Emparans/AWSD/Codigo/deteccion_de_objetos/modelo/BoxP_curve.png

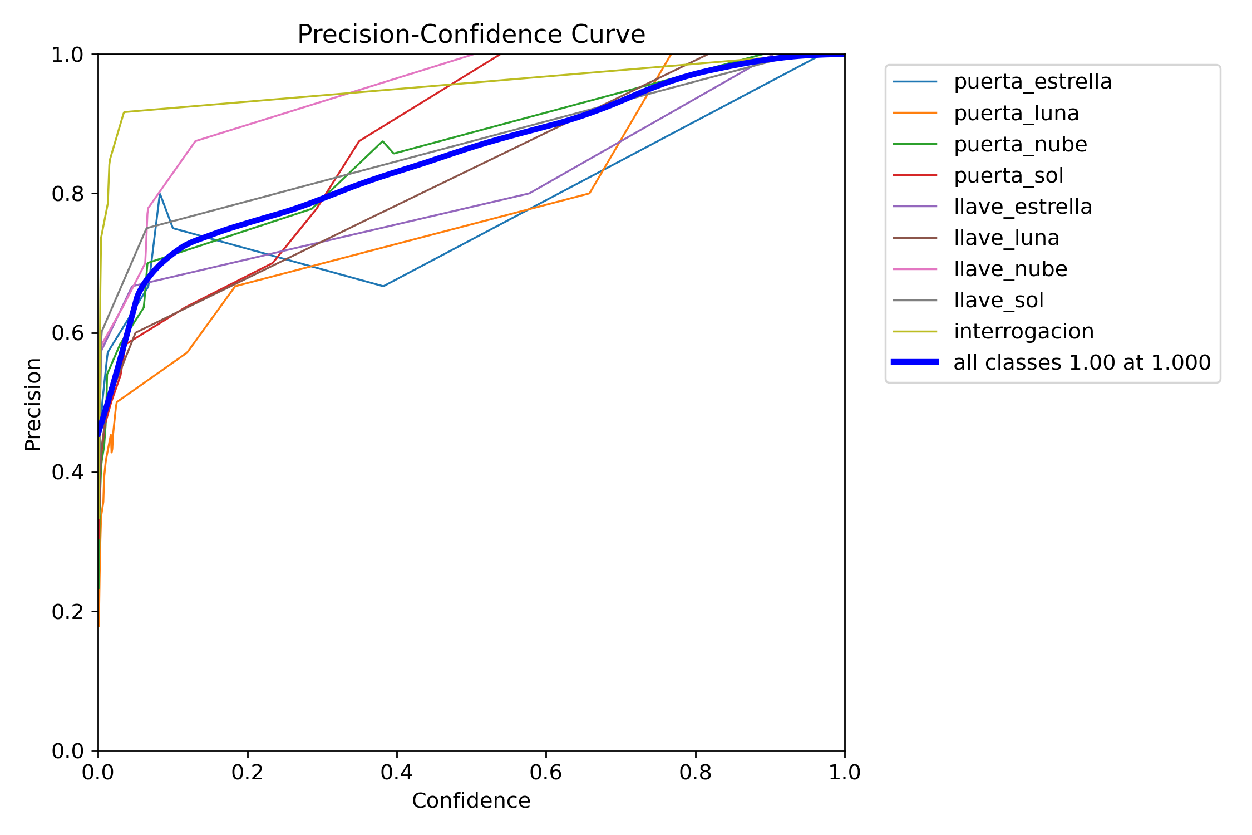
Codigo/deteccion_de_objetos/modelo/BoxP_curve.png
