Emparans/AWSD/Codigo/deteccion_de_objetos/modelo/BoxPR_curve.png

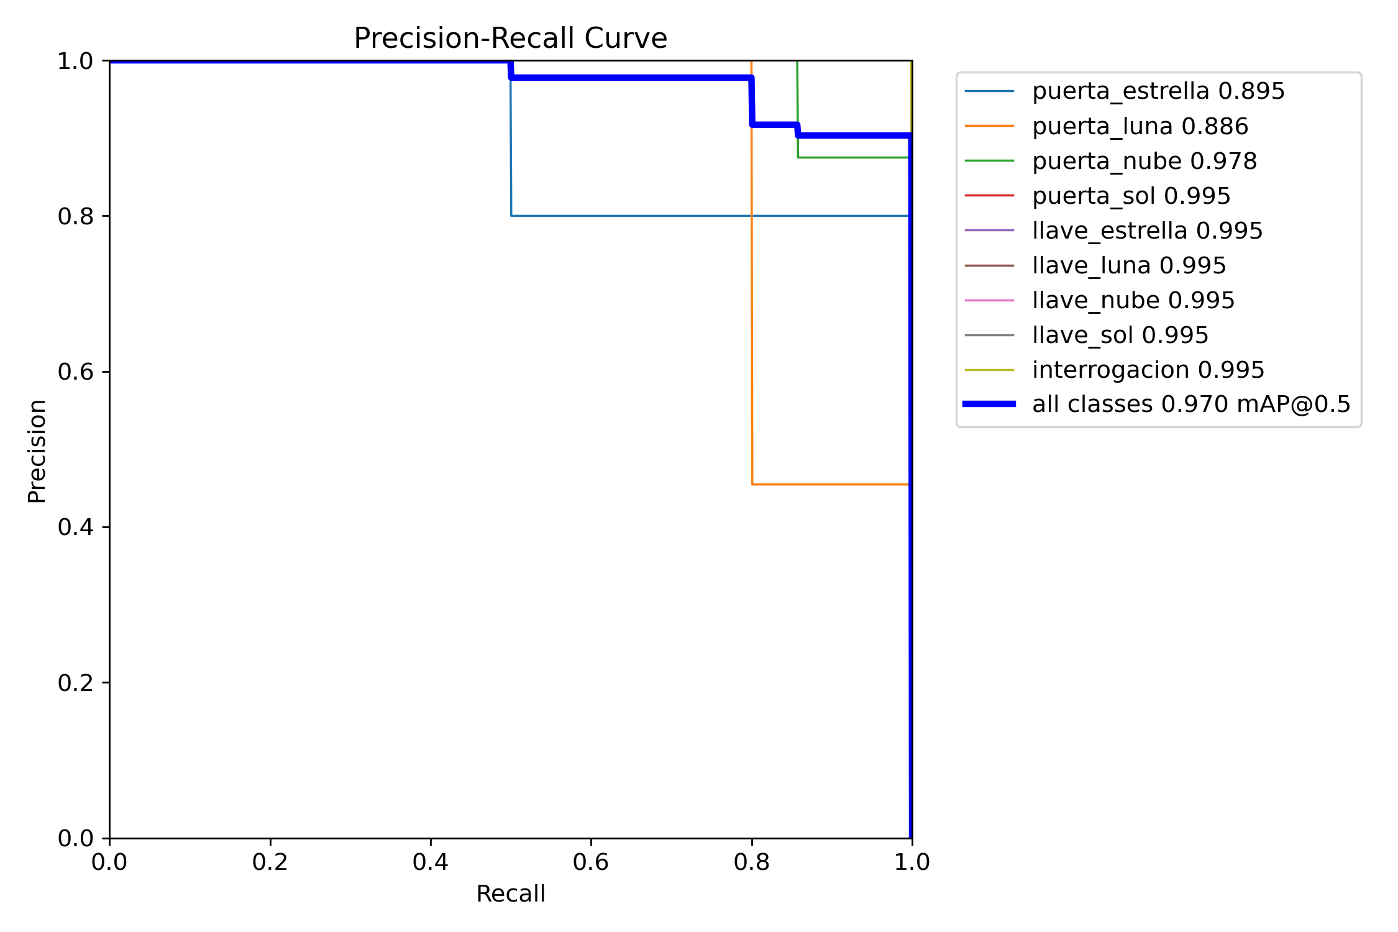
Codigo/deteccion_de_objetos/modelo/BoxPR_curve.png
