Emparans/AWSD/Codigo/deteccion_de_objetos/modelo/BoxR_curve.png

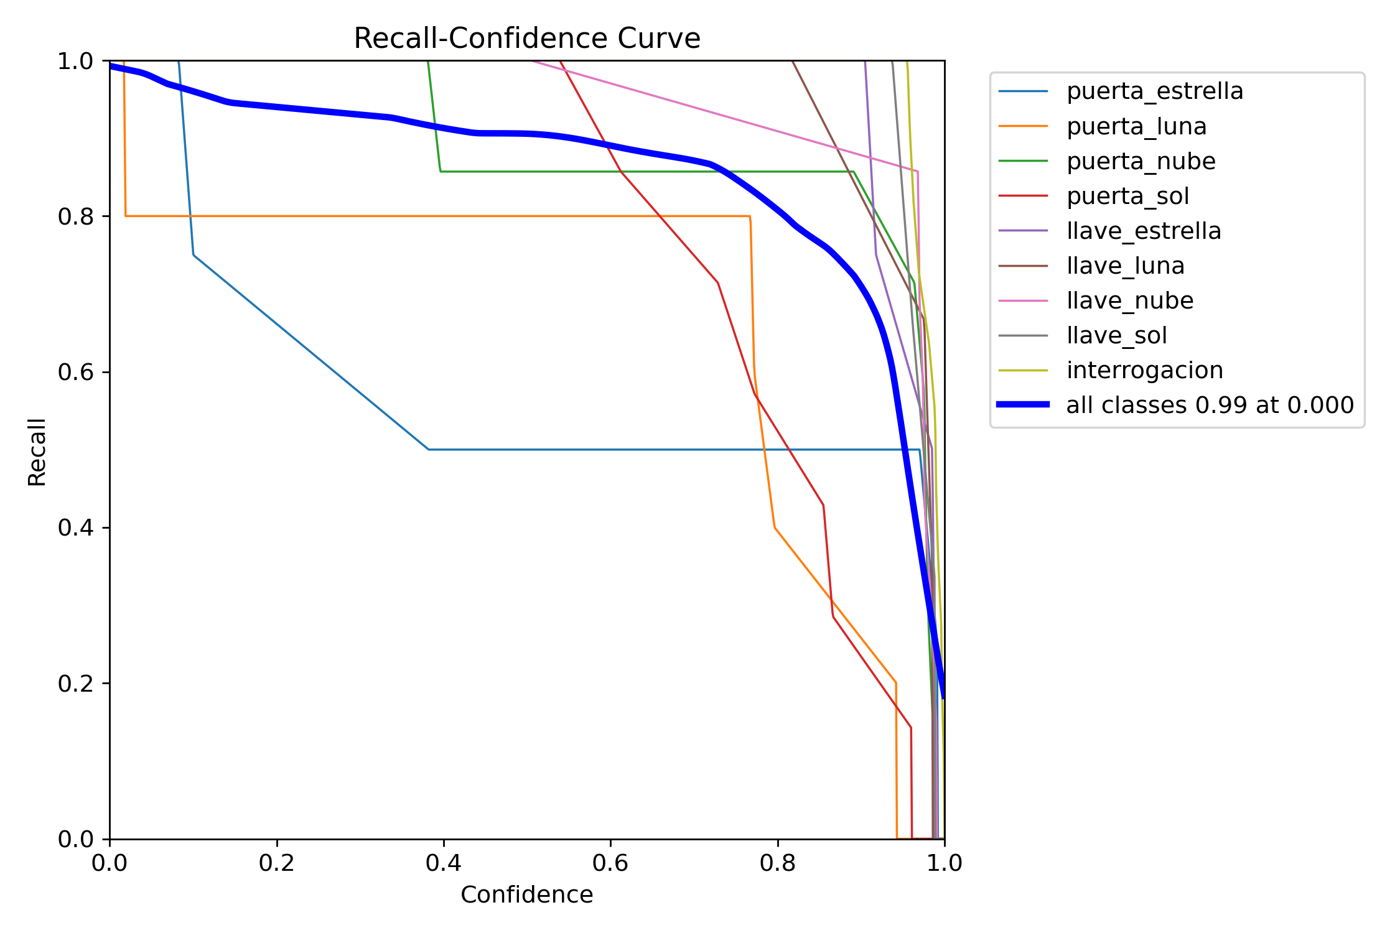
Codigo/deteccion_de_objetos/modelo/BoxR_curve.png
