Emparans/AWSD/Codigo/deteccion_de_objetos/modelo/confusion_matrix.png

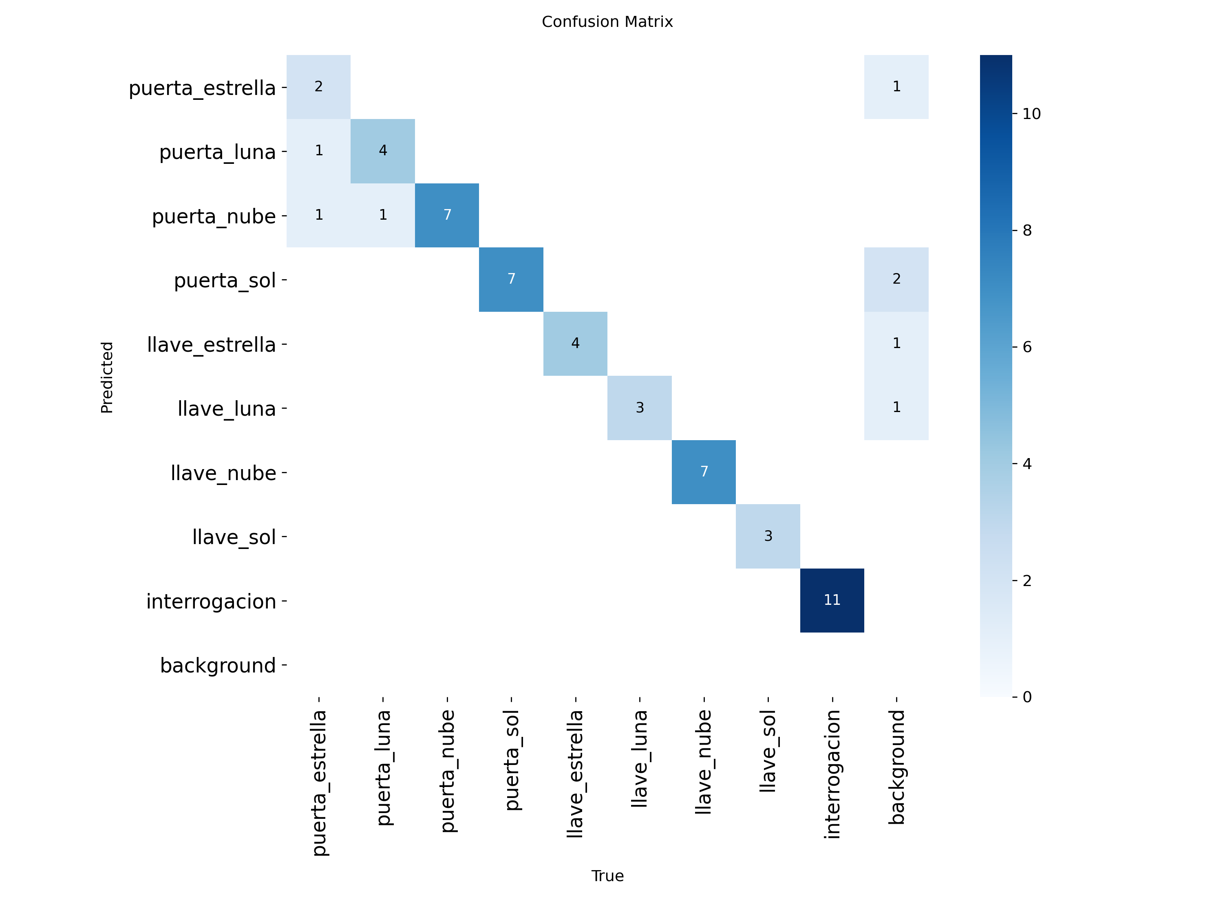
Codigo/deteccion_de_objetos/modelo/confusion_matrix.png
