Emparans/AWSD/Codigo/deteccion_de_objetos/modelo/labels.jpg

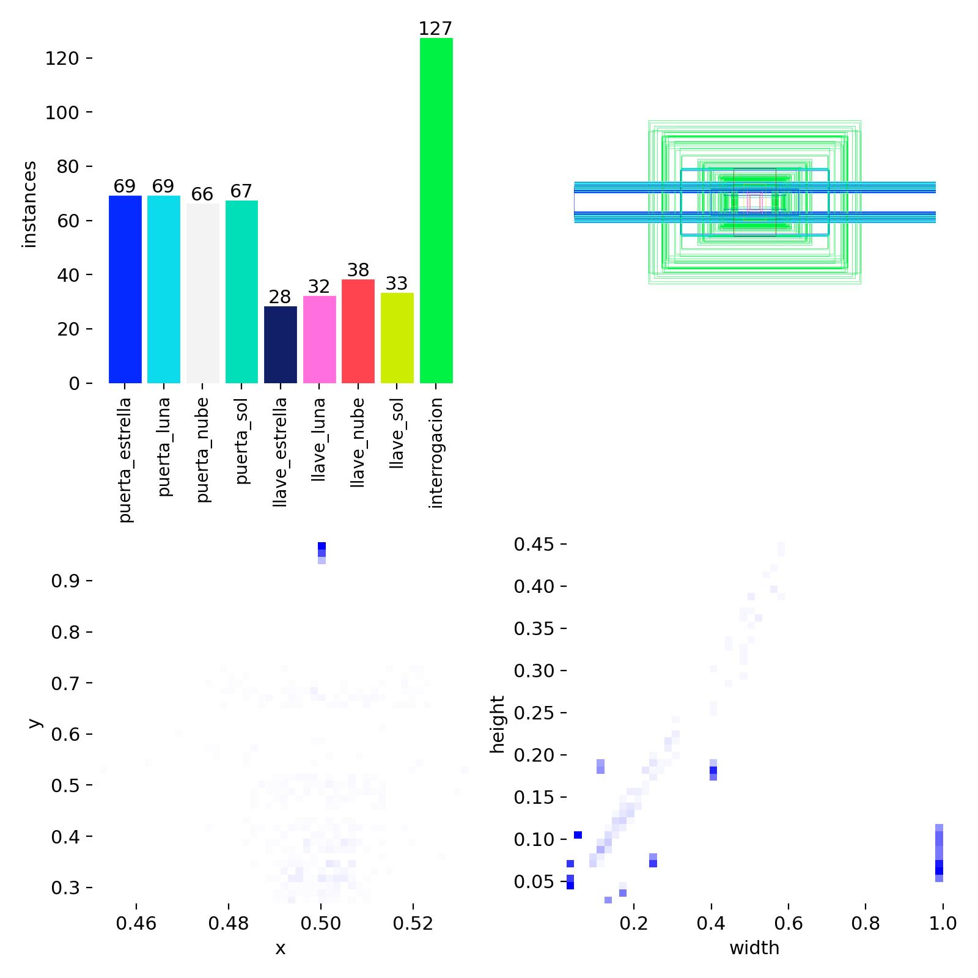
Codigo/deteccion_de_objetos/modelo/labels.jpg
