Emparans/AWSD/Codigo/deteccion_de_objetos/modelo/train_batch0.jpg

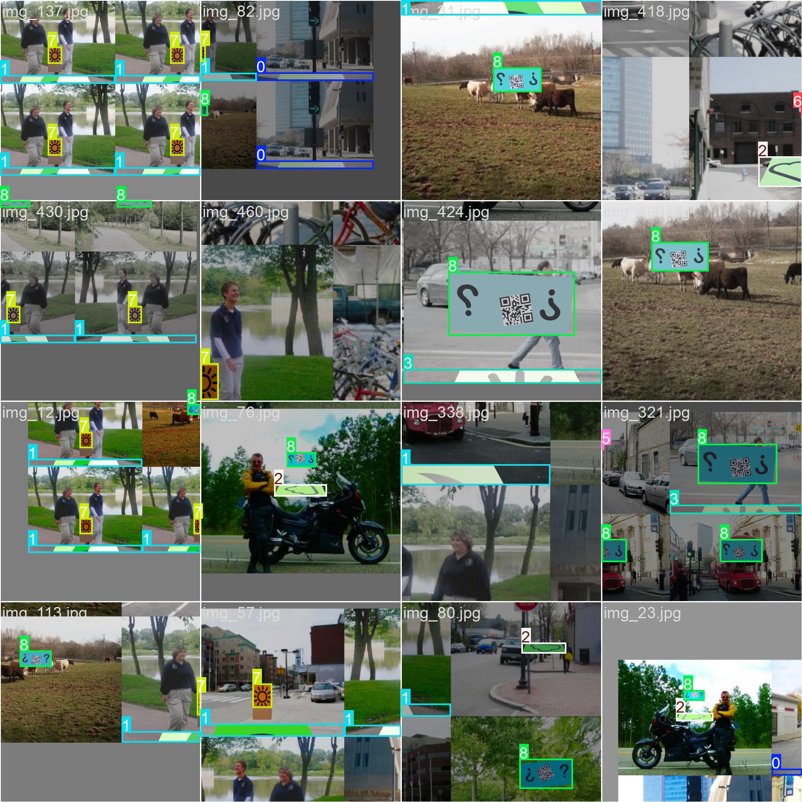
Codigo/deteccion_de_objetos/modelo/train_batch0.jpg
