Emparans/AWSD/Codigo/deteccion_de_objetos/modelo/train_batch1.jpg

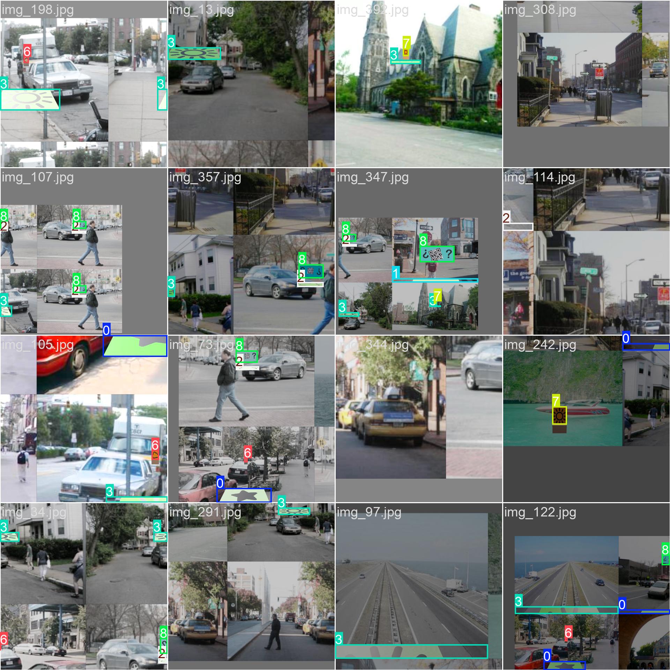
Codigo/deteccion_de_objetos/modelo/train_batch1.jpg
