Emparans/AWSD/Codigo/deteccion_de_objetos/modelo/train_batch2.jpg

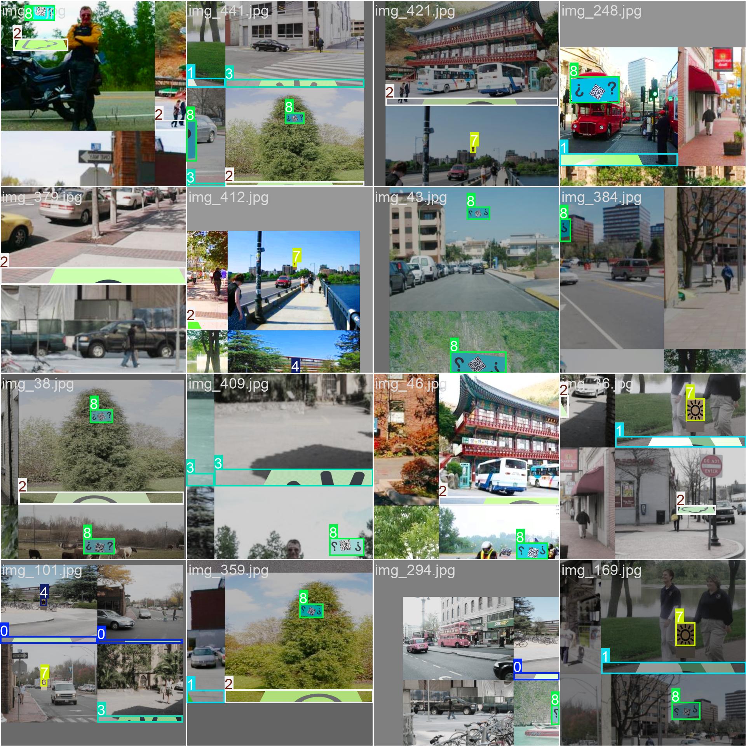
Codigo/deteccion_de_objetos/modelo/train_batch2.jpg
