Emparans/AWSD/Codigo/deteccion_de_objetos/modelo/train_batch1281.jpg

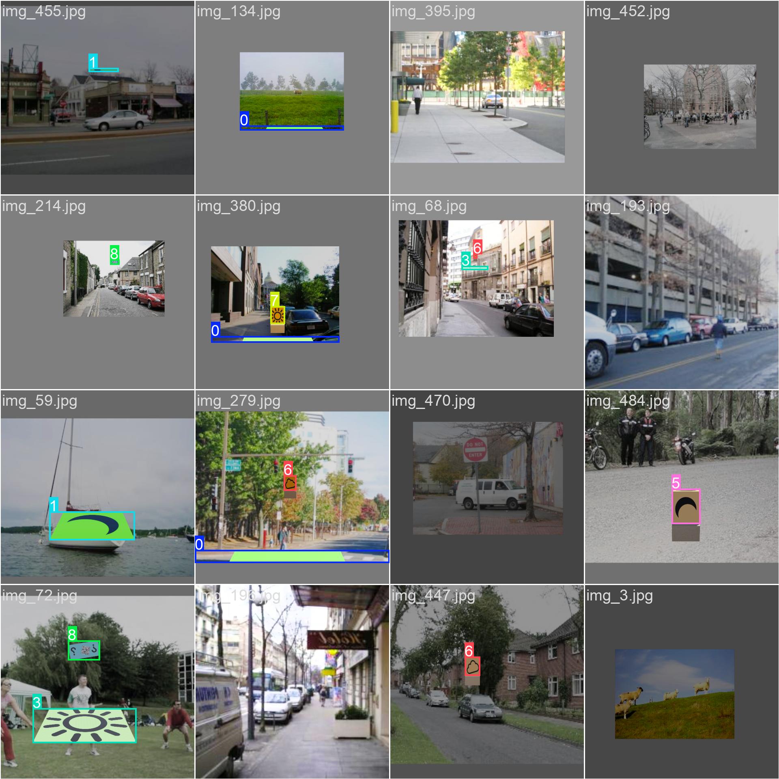
Codigo/deteccion_de_objetos/modelo/train_batch1281.jpg
