Emparans/AWSD/Codigo/deteccion_de_objetos/modelo/val/BoxF1_curve.png

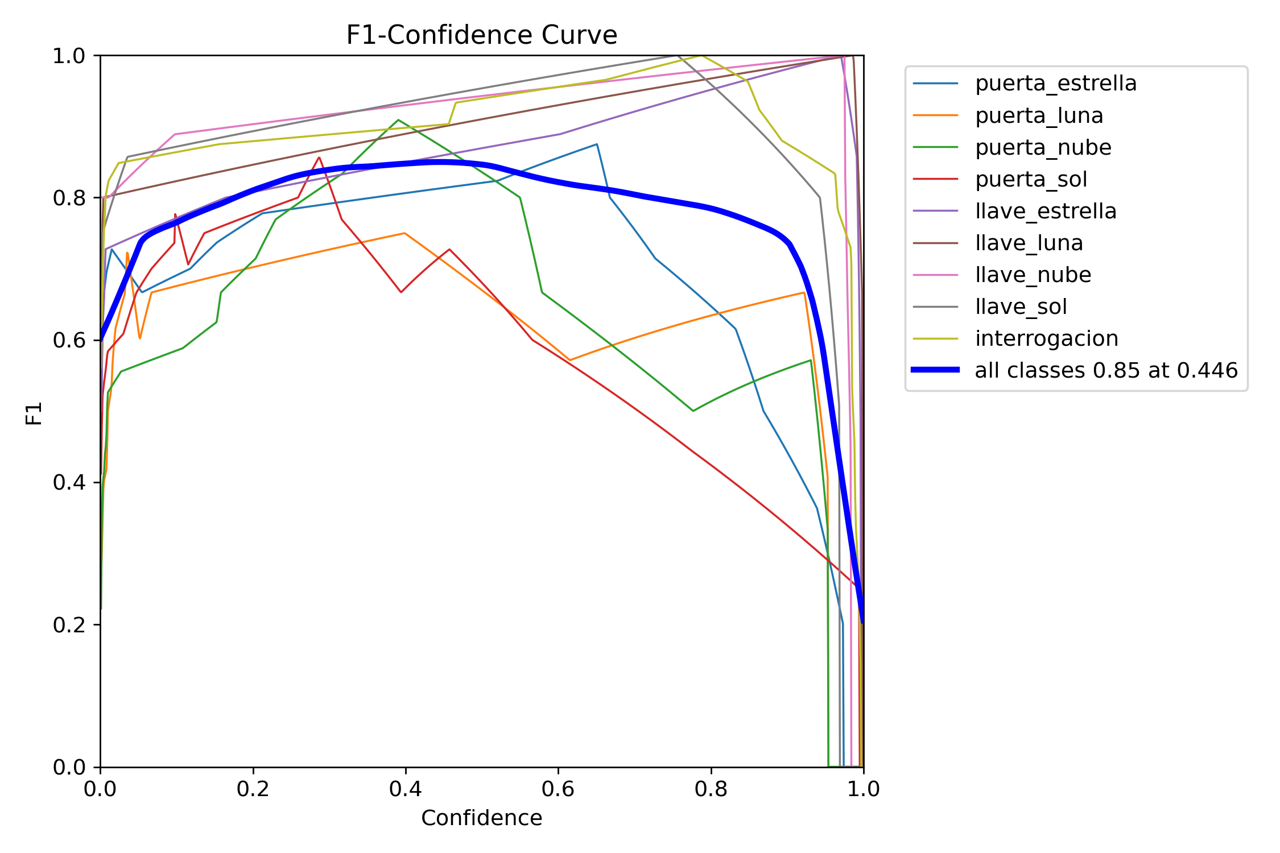
Codigo/deteccion_de_objetos/modelo/val/BoxF1_curve.png
