Emparans/AWSD/Codigo/deteccion_de_objetos/modelo/val/BoxP_curve.png

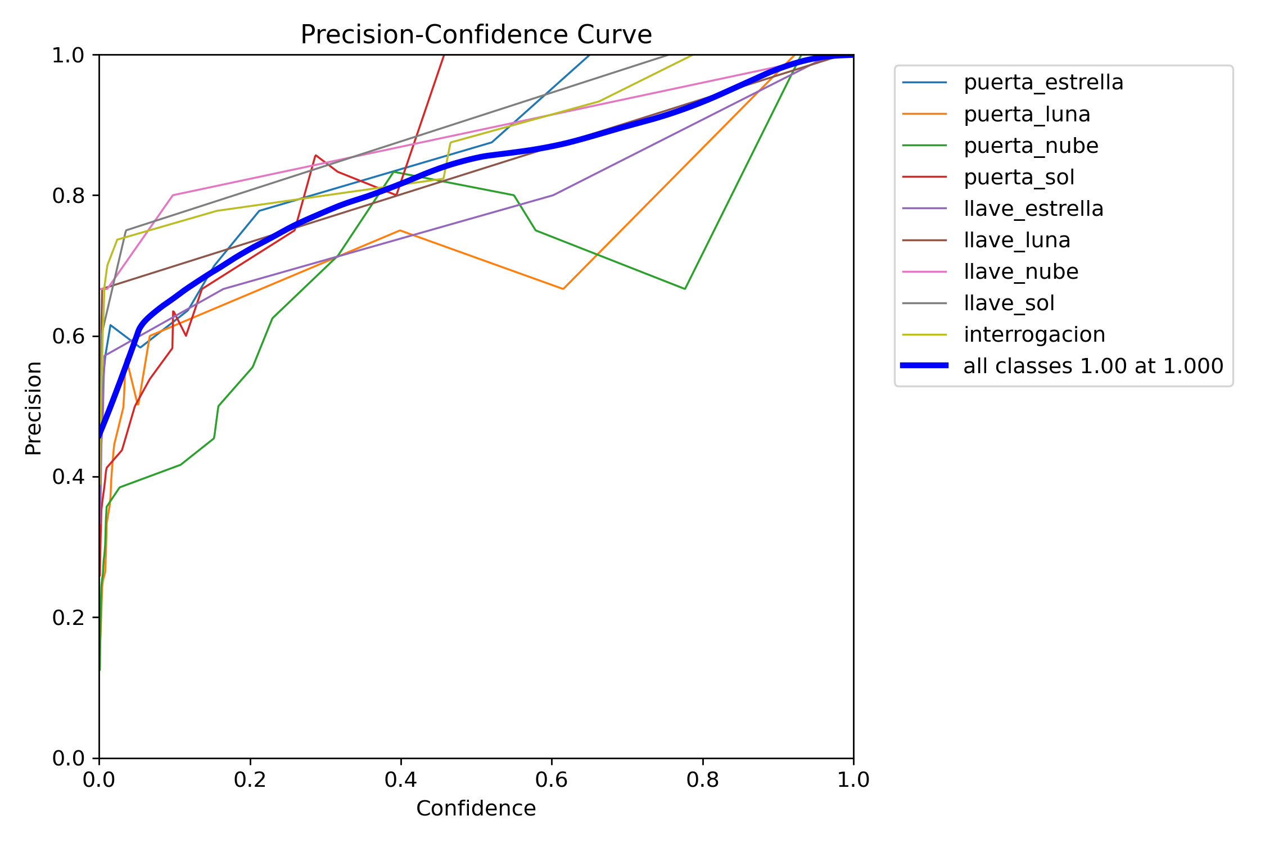
Codigo/deteccion_de_objetos/modelo/val/BoxP_curve.png
