Emparans/AWSD/Codigo/deteccion_de_objetos/modelo/val/BoxR_curve.png

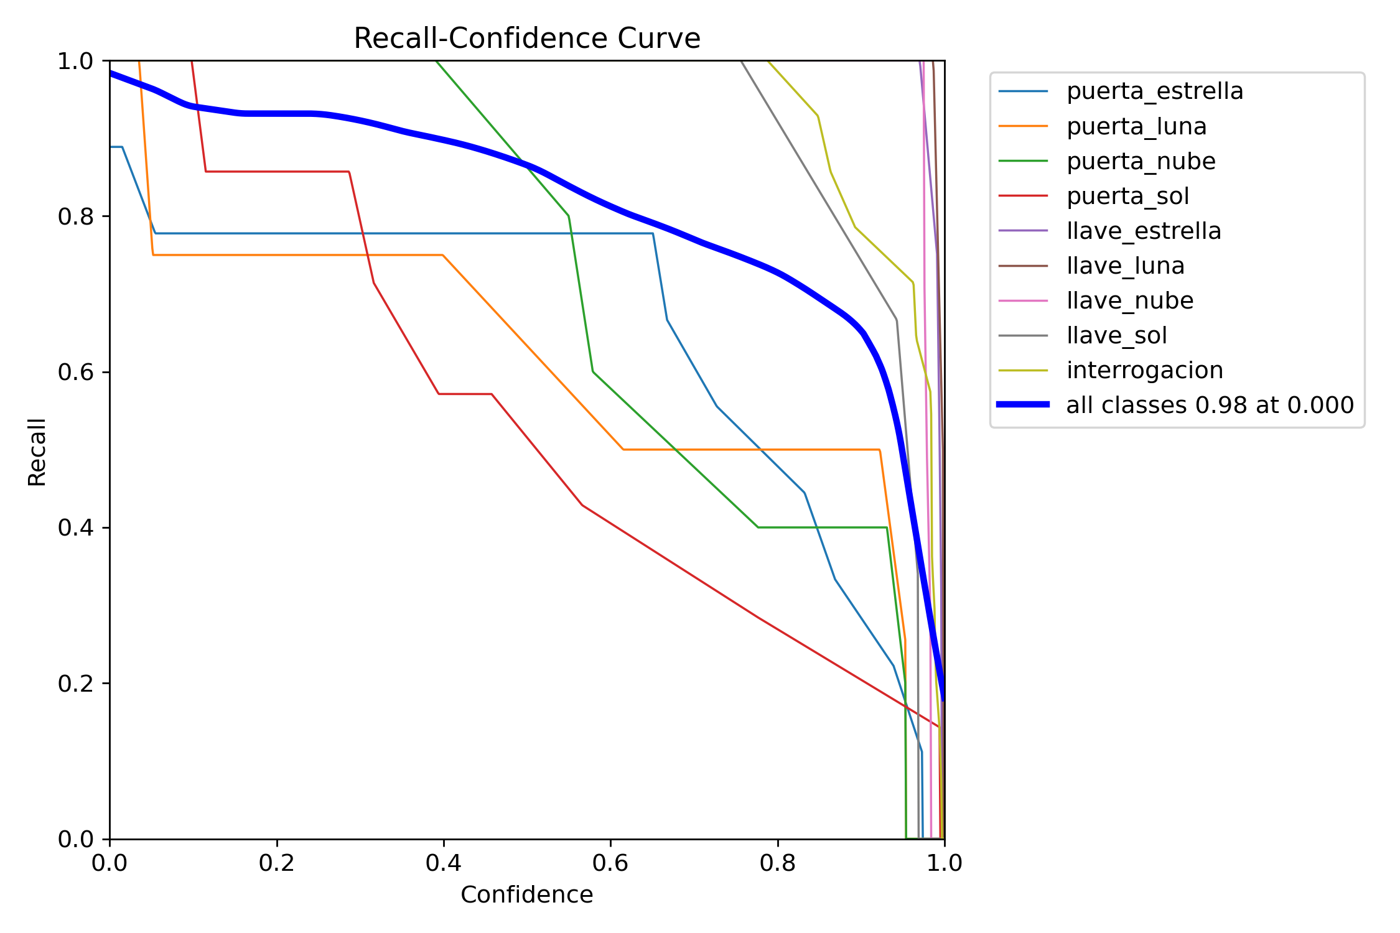
Codigo/deteccion_de_objetos/modelo/val/BoxR_curve.png
