Emparans/AWSD/Codigo/deteccion_de_objetos/modelo/val/val_batch2_labels.jpg

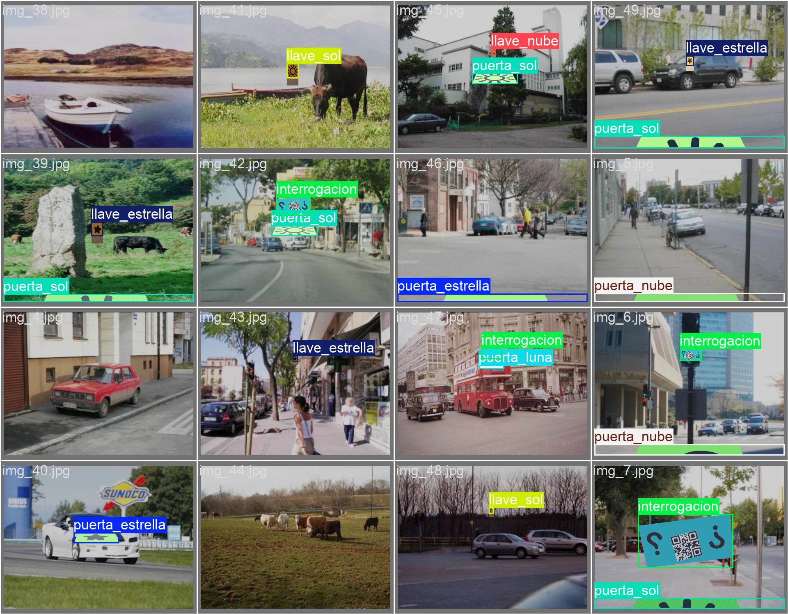
Codigo/deteccion_de_objetos/modelo/val/val_batch2_labels.jpg
