Emparans/AWSD/Codigo/deteccion_de_objetos/modelo/val_batch0_labels.jpg

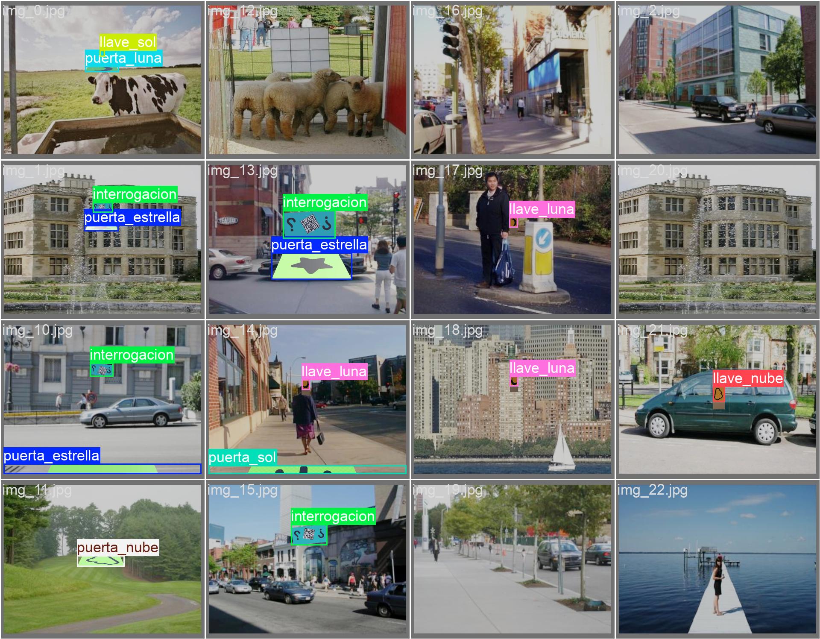
Codigo/deteccion_de_objetos/modelo/val_batch0_labels.jpg
