Emparans/AWSD/Codigo/deteccion_de_objetos/modelo/val_batch1_labels.jpg

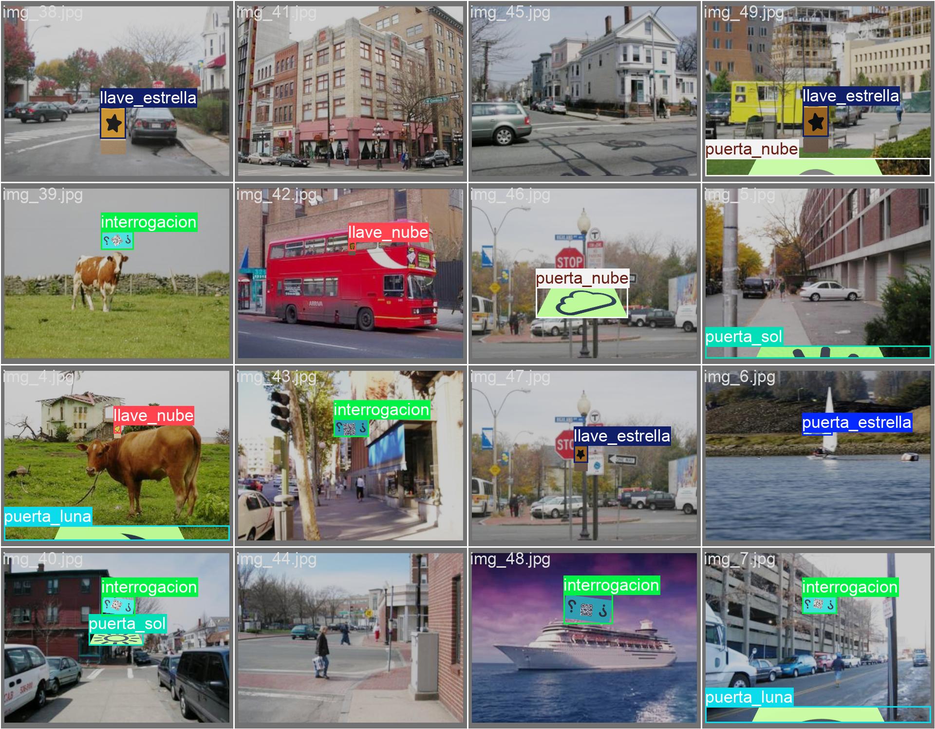
Codigo/deteccion_de_objetos/modelo/val_batch1_labels.jpg
