Emparans/AWSD/Codigo/deteccion_de_objetos/Texturas/estrella.jpg

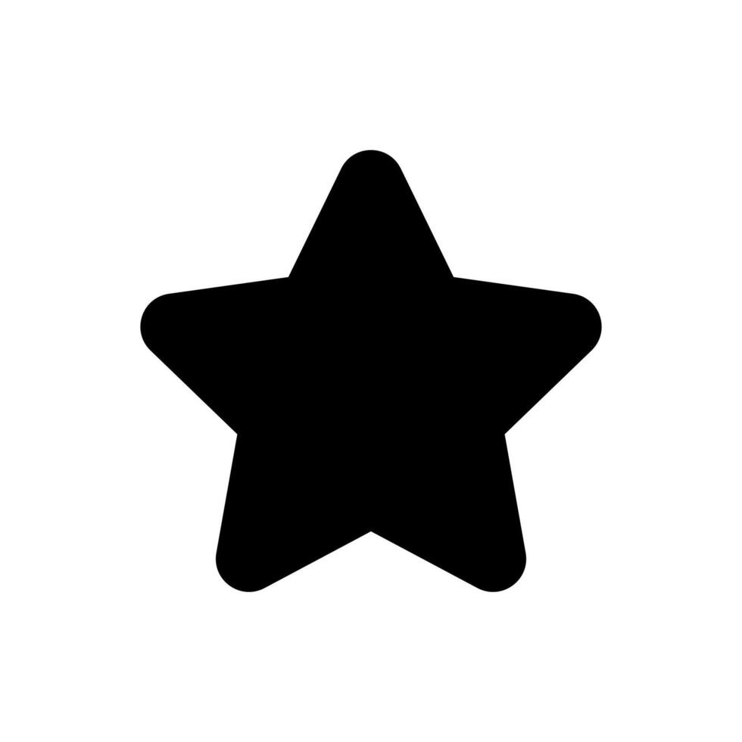
Codigo/deteccion_de_objetos/Texturas/estrella.jpg
