Emparans/AWSD/Codigo/deteccion_de_objetos/Texturas/interrogacion2.jpg

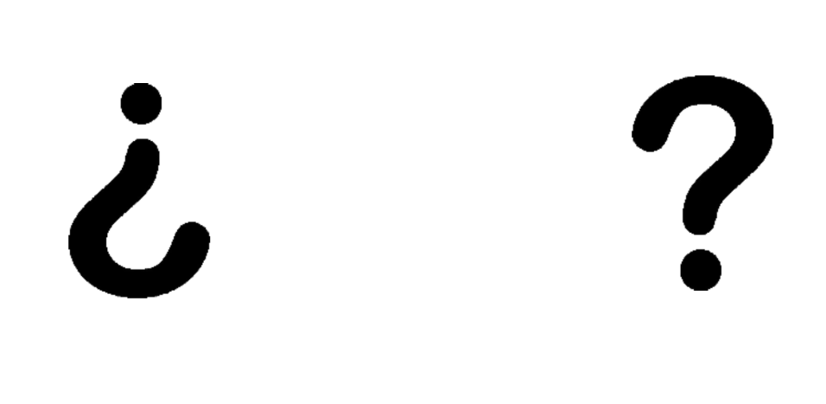
Codigo/deteccion_de_objetos/Texturas/interrogacion2.jpg
