Emparans/AWSD/Codigo/deteccion_de_objetos/Texturas/nube.jpg

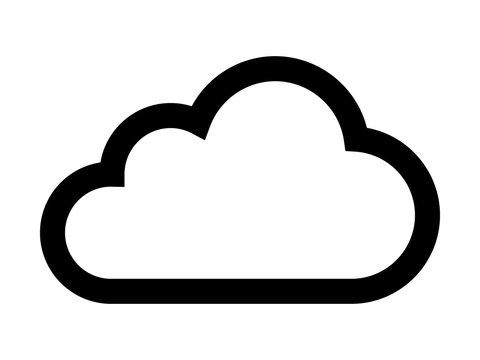
Codigo/deteccion_de_objetos/Texturas/nube.jpg
