Emparans/AWSD/Codigo/deteccion_de_objetos/Texturas/qr1.png

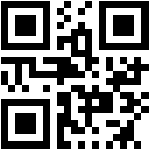
Codigo/deteccion_de_objetos/Texturas/qr1.png
