Emparans/AWSD/Codigo/deteccion_de_objetos/Texturas/qr2.png

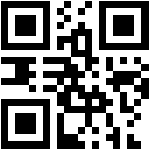
Codigo/deteccion_de_objetos/Texturas/qr2.png
