Emparans/AWSD/Codigo/deteccion_de_objetos/Texturas/qr4.png

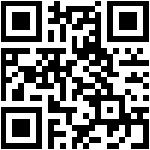
Codigo/deteccion_de_objetos/Texturas/qr4.png
