Emparans/AWSD/Codigo/deteccion_de_objetos/Texturas/qr5.png

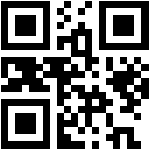
Codigo/deteccion_de_objetos/Texturas/qr5.png
