Emparans/AWSD/Codigo/deteccion_de_objetos/Texturas/qr6.png

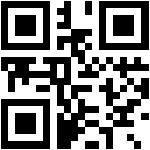
Codigo/deteccion_de_objetos/Texturas/qr6.png
