Emparans/AWSD/Codigo/deteccion_de_objetos/Texturas/qr7.png

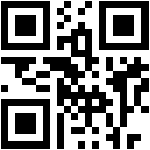
Codigo/deteccion_de_objetos/Texturas/qr7.png
