Emparans/AWSD/Codigo/deteccion_de_objetos/Texturas/qr8.png

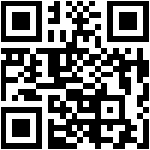
Codigo/deteccion_de_objetos/Texturas/qr8.png
