Emparans/AWSD/Codigo/deteccion_de_objetos/Texturas/suelo.jpg

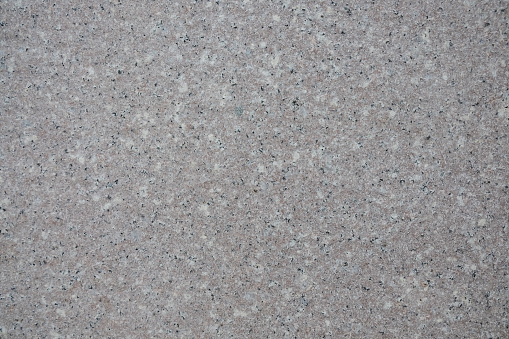
Codigo/deteccion_de_objetos/Texturas/suelo.jpg
