Emparans/AWSD/Fotos_proyecto/FotoLaberinto.jpeg

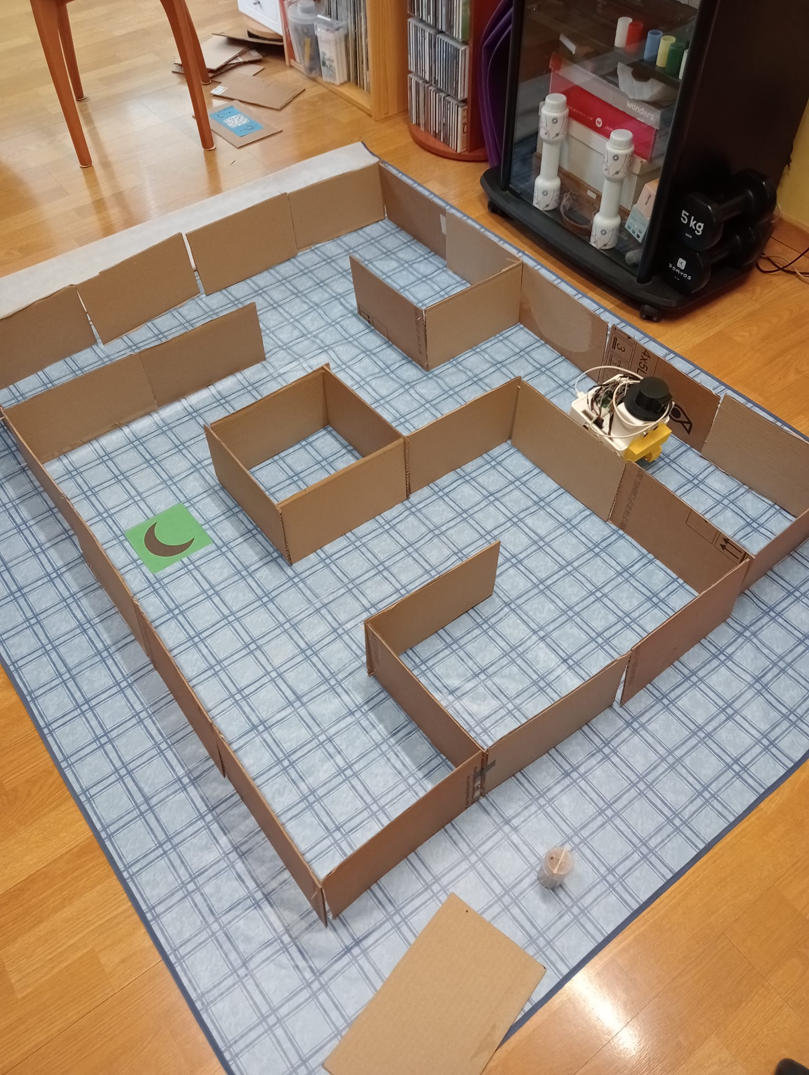
Fotos_proyecto/FotoLaberinto.jpeg
