Emparans/AWSD/Sim/img_dotted.jpg

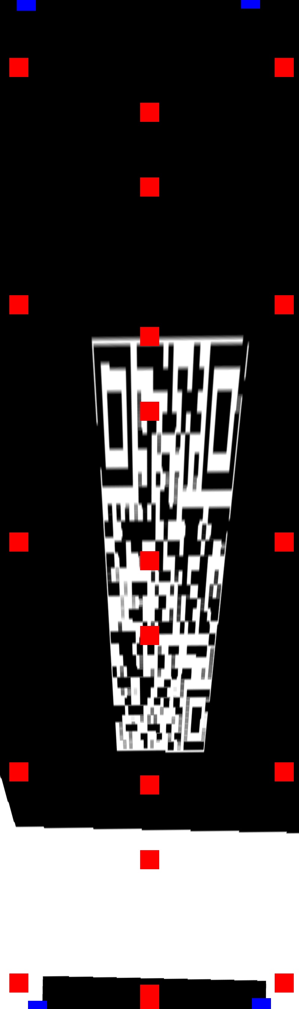
Sim/img_dotted.jpg
