Emparans/AWSD/Sim/org_dotted.jpg

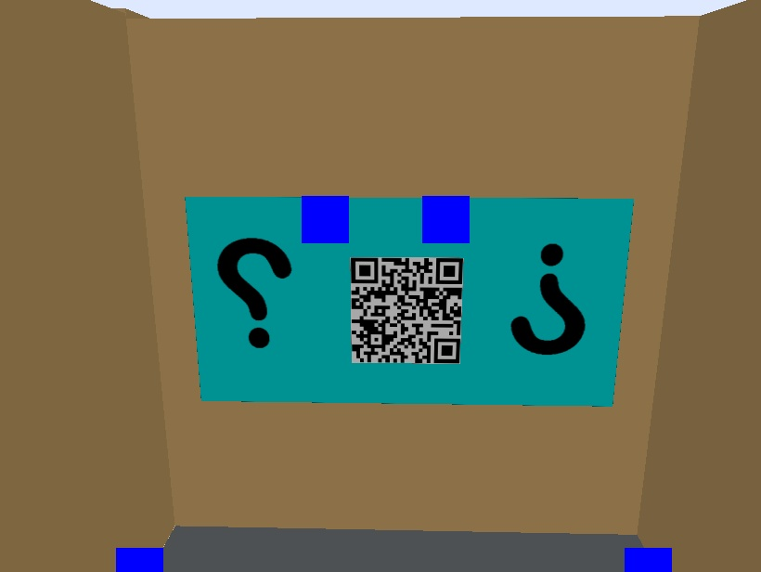
Sim/org_dotted.jpg
