Emparans/AWSD/Sim/texturas/preguntaBanderas.png

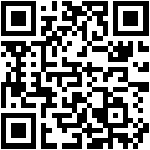
Sim/texturas/preguntaBanderas.png
