Emparans/AWSD/Sim/texturas/preguntaInstrumentos.png

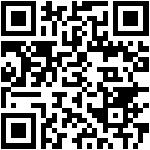
Sim/texturas/preguntaInstrumentos.png
