Emparans/AWSD/Sim/texturas/preguntaSalsa.png

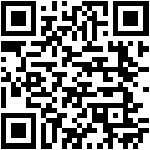
Sim/texturas/preguntaSalsa.png
