Emparans/AWSD/Codigo/deteccion_de_objetos/modelo/results.png

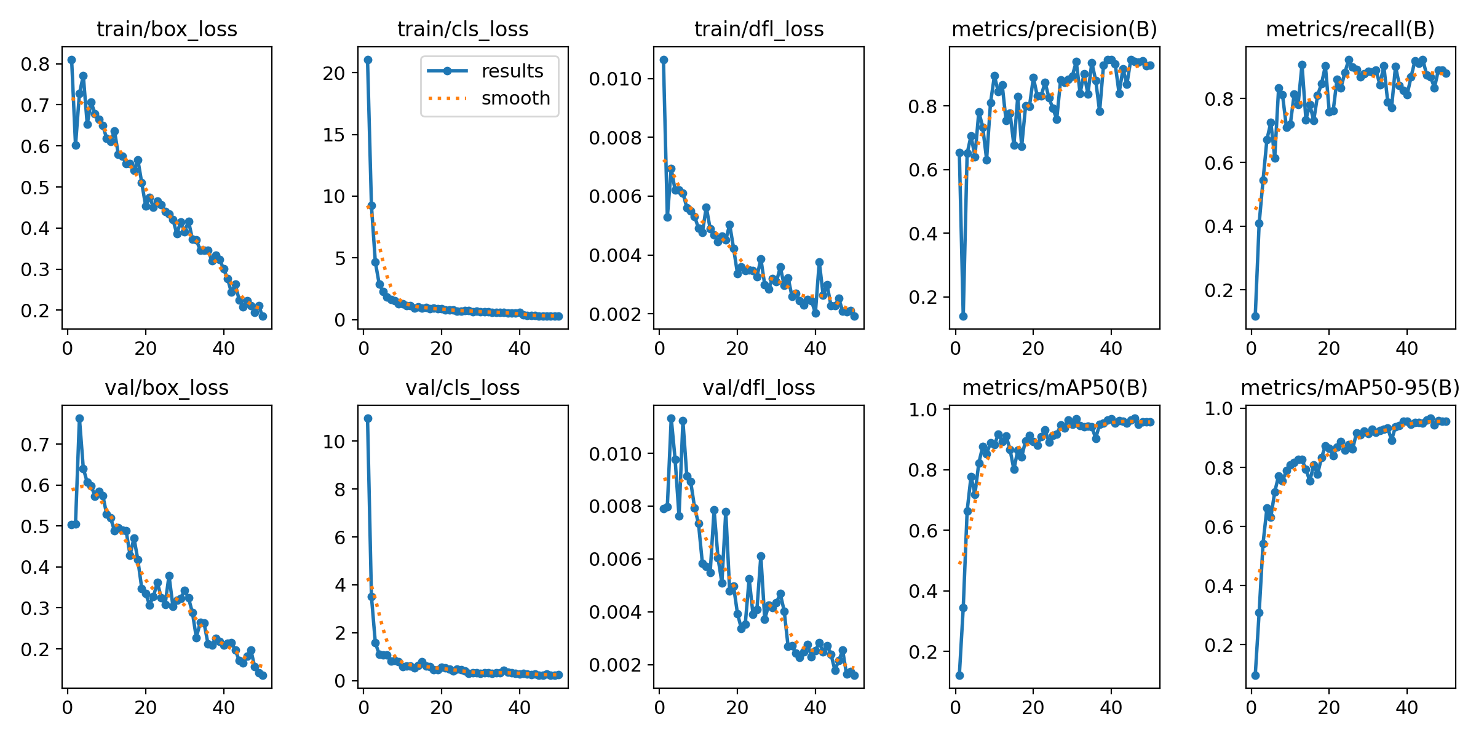
Codigo/deteccion_de_objetos/modelo/results.png
