Emparans/AWSD/Codigo/Código de pruebas unitarias/labyrinth.py

from collections import deque
import numpy as np
import cv2
import json
from pathlib import Path
from ultralytics import YOLO

dirs = ['u', 'r', 'd', 'l']

NAMES_TO_TYPES = {
    "interrogacion": "?",
    "llave": "K",
    "puerta": "D"
}

NAMES_TO_IDS = {
    "sol" : "0",
    "luna" : "1",
    "estrella" : "2",
    "nube" : "3"
}

ID_SYMBOLS = {
    "0": "☼", "sol": "☼",
    "1": "☾", "luna": "☾",     
    "2": "★", "estrella": "★",  
    "3": "☁", "nube": "☁"       
}

DISTANCES_DICTIONARY = {
    "interrogacion": [2.826, 5.426, 8.026, 10.626, 13.226],
    "llave": [2.742, 5.342, 7.942, 10.542, 13.142],
    "puerta": [1.6, 4.2, 6.8, 9.4, 12.0]
}

OBJECT_METRICS = {
    "interrogacion": {
        "2.826": {"w_dif": 0.183, "w_med": 0.494, "h_dif": 0.195, "h_med": 0.349},
        "5.426": {"w_dif": 0.098, "w_med": 0.268, "h_dif": 0.101, "h_med": 0.197},
        "8.026": {"w_dif": 0.071, "w_med": 0.18, "h_dif": 0.075, "h_med": 0.134},
        "10.626": {"w_dif": 0.049, "w_med": 0.139, "h_dif": 0.059, "h_med": 0.105},
        "13.226": {"w_dif": 0.04, "w_med": 0.111, "h_dif": 0.043, "h_med": 0.085}
    },
    "llave": {
        "2.742": {"w_dif": 0.002, "w_med": 0.115, "h_dif": 0.006, "h_med": 0.187},
        "5.342": {"w_dif": 0.001, "w_med": 0.062, "h_dif": 0.002, "h_med": 0.103},
        "7.942": {"w_dif": 0.001, "w_med": 0.042, "h_dif": 0.001, "h_med": 0.071},
        "10.542": {"w_dif": 0.001, "w_med": 0.032, "h_dif": 0.001, "h_med": 0.054},
        "13.142": {"w_dif": 0.001, "w_med": 0.026, "h_dif": 0.001, "h_med": 0.044}
    },
    "puerta": {
        "1.6": {"w_dif": 0.0, "w_med": 1.0, "h_dif": 0.107, "h_med": 0.089},
        "4.2": {"w_dif": 0.009, "w_med": 0.409, "h_dif": 0.026, "h_med": 0.185},
        "6.8": {"w_dif": 0.002, "w_med": 0.242, "h_dif": 0.011, "h_med": 0.076},
        "9.4": {"w_dif": 0.001, "w_med": 0.172, "h_dif": 0.006, "h_med": 0.041},
        "12.0": {"w_dif": 0.001, "w_med": 0.133, "h_dif": 0.004, "h_med": 0.026}
    }
}

interpretationSpots = np.array([
    #MIDDLE
    [400, 2660],
    [400, 2640],
    [400, 2300],
    [400, 2100],
    [400, 1700],
    [400, 1500],
    [400, 1100],
    [400,  900],
    [400,  500],
    [400,  300],

    #LEFT
    [50, 2630],
    [50, 2065],
    [50, 1450],
    [50,  815],
    [50,  180],

    #RIGHT
    [760, 2630],
    [760, 2065],
    [760, 1450],
    [760,  815],
    [760,  180]
], dtype=np.int32)

interpretationSpotsGT = np.array([
    #MIDDLE
    [118, 177],
    [238, 177],
    [358, 177],
    [478, 177],
    [598, 177],

    #LEFT
    [ 59, 123],
    [177, 123],
    [295, 123],
    [413, 123],
    [531, 123],

    #RIGHT
    [ 59, 243],
    [177, 243],
    [295, 243],
    [413, 243],
    [531, 243],
], dtype=np.int32)

class Node():
    def __init__(self):
        #Basic
        self.u = self.d = self.l = self.r  = None
        self.explored = False

        #Type related
        self.typeTile = 'X' # X = nothing K = Key, D = Door, ? = Question
        self.id = -1 # If it's a key or a door, it tracks the shape
        self.locked = False  # Just for doors, tracks its state
        self.dir = -1 # U = 0, R = 1, D = 2, L = 3, Relative to the map shown in web

        #Auxiliar
        self.prev = None
        self.coords = (-100, -100)

    def connect(self, x, y):
        self.coords = (x, y)

    def setTile(self, lab):
        x, y = self.coords
        if(self.u == None):
            if((x, y + 1) in lab.map):
                neighbor = lab.map[(x, y + 1)]
                self.u = neighbor
                neighbor.d = self
            else:
                lab.addPOI(self, 'u')

        if(self.d == None):
            if((x, y - 1) in lab.map):
                neighbor = lab.map[(x, y - 1)]
                self.d = neighbor
                neighbor.u = self
            else:
                lab.addPOI(self, 'd')
        if(self.l == None):
            if((x - 1, y) in lab.map):
                neighbor = lab.map[(x - 1, y)]
                self.l = neighbor
                neighbor.r = self
            else:
                lab.addPOI(self, 'l')
        if(self.r == None):
            if((x + 1, y) in lab.map):
                neighbor = lab.map[(x + 1, y)]
                self.r = neighbor
                neighbor.l = self
            else:
                lab.addPOI(self, 'r')

class POI():
    def __init__(self, tile, dirToLook, h = -1):
        self.tile = tile
        self.dirToLook = dirToLook #U, D, L, R
        self.h = h
        self.time = 0
        self.type = -1

    def calculateHeuristic(self, currentNode):
        tx, ty = self.tile.coords
        cx, cy = currentNode.coords
        dist = abs(tx - cx) + abs(ty - cy)
        timeScaleFactor = np.sqrt(2) / 8
        self.h = max( dist - (timeScaleFactor * self.time), 0)
        self.time += 1

class Labyrinth():
    def __init__(self, nOfQuests):
        self.map = {}
        self.poi = []
        self.prioritypoi = []
        self.foundIDs = []
        
        self.remainingQuests = nOfQuests
        self.mapRemain = 36 #I assume that the map's always gonna be a 6x6

        self.score = 0

        self.currentPos = (0, 0)
        self.currentDir = 'r'
        self.currentNode = None
        self.held = -1 # Id of the key the robot is carrying, -1 if none

    def addPOI(self, tile, dirToLook, isID = False):
        if(isID):
            if not any(p.tile == tile for p in self.foundIDs):
                self.foundIDs.append(POI(tile, dirToLook, 1))
        else:
            if not any(p.tile == tile and p.dirToLook == dirToLook for p in self.poi):
                self.poi.append(POI(tile, dirToLook))

    def goToPoi(self):
        if not self.poi and not self.prioritypoi:
            return 'X', []

        if(len(self.prioritypoi) > 0):
            dest = self.prioritypoi.pop(0)
        else:
            dest = self.poi.pop(0)

        if dest.tile.typeTile == 'X' and getattr(dest.tile, dest.dirToLook) is not None:
            return self.goToPoi()

        for m in self.map.values():
            m.prev = None
        
        self.currentNode.prev = self.currentNode

        bfs = deque()
        bfs.append(self.currentNode)

        found = False
        if self.currentNode == dest.tile:
            found = True

        while bfs and not found:
            c = bfs.popleft()

            for dir in dirs:
                n = getattr(c, dir)

                if (isinstance(n, Node) and (n.explored == True) and (n.prev == None)):
                    n.prev = c
                    if(n == dest.tile):
                        found = True
                        break
                    else:
                        bfs.append(n)
                
        if(found):
            n = dest.tile
            path = deque()
            while n != self.currentNode:
                path.append(n)
                n = n.prev
            
            #n = currentnode here

            commands = [] # f- n forwards, l- turn left + n forwards, r- turn right + n forwards, b- double turn right + n forwards
            lastcommand = self.currentDir

            while path:
                if n.u == path[-1]:
                    if lastcommand == 'u':
                        commands.append("f")
                    elif lastcommand == 'r':
                        commands.append("l")
                    elif lastcommand == 'd':
                        commands.append("b")
                    elif lastcommand == 'l':
                        commands.append("r")
                    lastcommand = 'u'

                elif n.r == path[-1]:
                    if lastcommand == 'u':
                        commands.append("r")
                    elif lastcommand == 'r':
                        commands.append("f")
                    elif lastcommand == 'd':
                        commands.append("l")
                    elif lastcommand == 'l':
                        commands.append("b")
                    lastcommand = 'r'

                elif n.d == path[-1]:
                    if lastcommand == 'u':
                        commands.append("b")
                    elif lastcommand == 'r':
                        commands.append("r")
                    elif lastcommand == 'd':
                        commands.append("f")
                    elif lastcommand == 'l':
                        commands.append("l")
                    lastcommand = 'd'

                elif n.l == path[-1]:
                    if lastcommand == 'u':
                        commands.append("l")
                    elif lastcommand == 'r':
                        commands.append("b")
                    elif lastcommand == 'd':
                        commands.append("r")
                    elif lastcommand == 'l':
                        commands.append("f")
                    lastcommand = 'l'
                
                n = path.pop()                

            ppcomands = []
            for cmd in commands:
                if cmd in ['l', 'r', 'b']:
                    ppcomands.append([cmd, 1])
                    
                elif cmd == 'f':
                    if len(ppcomands) == 0:
                        ppcomands.append(['f', 1])
                    else:
                        ppcomands[-1][1] += 1

            if lastcommand != dest.dirToLook:
                turn_map = {
                    ('u', 'l'): 'l', ('u', 'r'): 'r', ('u', 'd'): 'b',
                    ('d', 'r'): 'l', ('d', 'l'): 'r', ('d', 'u'): 'b',
                    ('l', 'd'): 'l', ('l', 'u'): 'r', ('l', 'r'): 'b',
                    ('r', 'u'): 'l', ('r', 'd'): 'r', ('r', 'l'): 'b'
                }
                needed_turn = turn_map.get((lastcommand, dest.dirToLook))
                if needed_turn:
                    ppcomands.append([needed_turn, 0])

            #Will be updated elsewhere, in real time as the robot moves forward. This is only for debug purposes
            self.currentNode = dest.tile
            self.currentPos = dest.tile.coords
            self.currentDir = dest.dirToLook
            
            # We will send this to the robot. The output looks like: [['r', 2], ['r', 1], ['l', 3]]. We first send the typeTile though, to know what to do next.
            return dest.tile.typeTile, ppcomands #The typeTiles 'X' and 'D' should expect an image later, the other 2 just select the next POI and keep going.

        else:
            print(f"Camí de {self.currentNode} cap a {dest.tile} no trobat.")
            return self.selectNextPOI()        
            
    def selectNextPOI(self):
        if(not self.poi and not self.prioritypoi):
            return ('X', [])
        
        for p in self.poi:
            p.calculateHeuristic(self.currentNode)
            
        self.poi.sort(key=lambda x: x.h, reverse=False)
        self.prioritypoi.sort(key=lambda x: x.h, reverse=False)
        return self.goToPoi()

    def updateFromImage(self, imgName, mostRestrictiveDoor):
        input_path = f"{Path(__file__).parent}/testOutput/{imgName}_cenitalBW.jpg"

        img = cv2.imread(input_path)
        if img is None:
            print(f"No se pudo cargar la imagen en {input_path}")
            exit()

        #Process path
        k = 25 #Pixels to check around the interpretationSpots (2 = 5x5 area, 3 = 7x7 area, 25 = 51x51...)
        th = 0.4

        prev = self.currentNode
        coords = list(self.currentPos)
        dir = self.currentDir
        tilesToUpdate = deque()
        maxdist = min(5, mostRestrictiveDoor)
        for i in range(0, 2*maxdist, 2):
            pt1 = interpretationSpots[i]
            pt2 = interpretationSpots[i + 1]

            if(dir == 'u'):
                coords[1] += 1
            elif (dir == 'd'):
                coords[1] -= 1
            elif(dir == 'l'):
                coords[0] -= 1
            elif (dir == 'r'):
                coords[0] += 1

            current_coords = tuple(coords)

            tile = True
            
            px, py = pt1
            y1 = max(0, py - (k * 5))
            y2 = min(img.shape[0], py + (k * 5) + 1)
            x1 = max(0, px - (k * 5))
            x2 = min(img.shape[1], px + (k * 5) + 1)
            roi = img[y1:y2, x1:x2]
            tile = np.mean(roi < 128) > 0.6

            if(tile):
                px, py = pt2
                y1 = max(0, py - (k * 5))
                y2 = min(img.shape[0], py + (k * 5) + 1)
                x1 = max(0, px - (k * 5))
                x2 = min(img.shape[1], px + (k * 5) + 1)
                roi = img[y1:y2, x1:x2]
                tile = np.mean(roi < 128) > 0.6

            if(tile):
                if(current_coords not in self.map):
                    n = Node()
                    self.map[current_coords] = n
                    n.connect(current_coords[0], current_coords[1])
                    self.mapRemain -= 1
                else:
                    n = self.map[current_coords]
                
                setattr(prev, dir, n)
                if(dir == 'u'):
                    setattr(n, 'd', prev)
                elif (dir == 'd'):
                    setattr(n, 'u', prev)
                elif(dir == 'l'):
                    setattr(n, 'r', prev)
                elif (dir == 'r'):
                    setattr(n, 'l', prev)
                
                prev = n
                tilesToUpdate.append(n)
            else:
                break


        if   dir == 'u' and prev.u is None and maxdist == 5: prev.u = 'Wall'
        elif dir == 'd' and prev.d is None and maxdist == 5: prev.d = 'Wall'
        elif dir == 'l' and prev.l is None and maxdist == 5: prev.l = 'Wall'
        elif dir == 'r' and prev.r is None and maxdist == 5: prev.r = 'Wall'

        #Add Walls
        for i, t in enumerate(tilesToUpdate):
            #Left
            px, py = interpretationSpots[i + 10]

            y1 = max(0, py - k)
            y2 = min(img.shape[0], py + k + 1)
            x1 = max(0, px - k)
            x2 = min(img.shape[1], px + k + 1)

            roi = img[y1:y2, x1:x2]

            is_tile = np.mean(roi < 128) > th

            if(not is_tile):
                if(dir == 'u' and t.l is None):
                    t.l = 'Wall'
                elif (dir == 'd' and t.r is None):
                    t.r = 'Wall'
                elif(dir == 'l' and t.d is None):
                    t.d = 'Wall'
                elif (dir == 'r' and t.u is None):
                    t.u = 'Wall'

            #Right
            px, py = interpretationSpots[i + 15]
            y1 = max(0, py - k)
            y2 = min(img.shape[0], py + k + 1)
            x1 = max(0, px - k)
            x2 = min(img.shape[1], px + k + 1)

            roi = img[y1:y2, x1:x2]

            is_tile = np.mean(roi < 128) > th

            if(not is_tile):
                if(dir == 'u' and t.r is None):
                    t.r = 'Wall'
                elif (dir == 'd' and t.l is None):
                    t.l = 'Wall'
                elif(dir == 'l' and t.u is None):
                    t.u = 'Wall'
                elif (dir == 'r' and t.d is None):
                    t.d = 'Wall'

        #Process inverse path to set tiles
        while len(tilesToUpdate) > 0:
            t = tilesToUpdate.pop()
            t.setTile(self)

        # VIEW & SAVE DOTTED IMAGE
        # for i, pt in enumerate(interpretationSpots):
        #     cv2.circle(
        #         img,
        #         tuple(pt.astype(int)),
        #         k,
        #         (0, 0, 255),
        #         -1
        #     )

        # output_path = f"{Path(__file__).parent}/testOutput/{imgName}_cenitalBWDotted.png"
        # cv2.imwrite(output_path, img)
        # cv2.imshow(imgName, img)        
        # cv2.waitKey(0)

        return
            
    def printLab(self):
        if not self.map:
            return "Empty Map"

        min_x = min(x for x, y in self.map.keys())
        max_x = max(x for x, y in self.map.keys())
        min_y = min(y for x, y in self.map.keys())
        max_y = max(y for x, y in self.map.keys())

        cols = (max_x - min_x + 1) * 4 + 1
        rows = (max_y - min_y + 1) * 2 + 1
        
        grid = [[' ' for _ in range(cols)] for _ in range(rows)]

        poi_coords = {p.tile.coords for p in self.poi if hasattr(p.tile, 'coords')}
        
        dir_chars = {'u': '^', 'd': 'v', 'l': '<', 'r': '>'}

        for (x, y), node in self.map.items():
            if node.explored == False:
                continue

            cx = (x - min_x) * 4 + 2
            cy = (max_y - y) * 2 + 1

            # Draw Corners
            grid[cy-1][cx-2] = '+'
            grid[cy-1][cx+2] = '+'
            grid[cy+1][cx-2] = '+'
            grid[cy+1][cx+2] = '+'

            # Draw Center (Robot, POI, or empty space)
            if (x, y) == self.currentPos:
                grid[cy][cx] = dir_chars.get(self.currentDir, 'R')
            elif (x, y) in poi_coords:
                grid[cy][cx] = '*'
            else:
                grid[cy][cx] = '.'

            if node.typeTile != 'X':
                grid[cy][cx-1] = node.typeTile
                
                if node.id != -1:
                    grid[cy][cx+1] = ID_SYMBOLS.get(str(node.id), str(node.id))

            u_char = '-' if node.u == 'Wall' else '?' if node.u is None else ' '
            grid[cy-1][cx-1] = u_char
            grid[cy-1][cx]   = u_char
            grid[cy-1][cx+1] = u_char

            d_char = '-' if node.d == 'Wall' else '?' if node.d is None else ' '
            grid[cy+1][cx-1] = d_char
            grid[cy+1][cx]   = d_char
            grid[cy+1][cx+1] = d_char

            l_char = '|' if node.l == 'Wall' else '?' if node.l is None else ' '
            grid[cy][cx-2] = l_char

            r_char = '|' if node.r == 'Wall' else '?' if node.r is None else ' '
            grid[cy][cx+2] = r_char

        return("\n".join("".join(row) for row in grid))
    
    def toJSON(self):
        nodes_list = []
        for coords, node in self.map.items():
            sprite = 0
            if node.u == 'Wall': sprite += 1
            if node.r == 'Wall': sprite += 2
            if node.d == 'Wall': sprite += 4
            if node.l == 'Wall': sprite += 8

            nodes_list.append({
                "coords": list((coords[0], coords[1])),
                "explored": node.explored,
                "typeTile": node.typeTile,
                "id": node.id,
                "locked": node.locked,
                "sprite": sprite
            })

        payload = {
            "state": {
                "remainingQuests": self.remainingQuests,
                "mapRemain": self.mapRemain,
                "score": self.score
            },
            "robot": {
                "currentPos": list(self.currentPos),
                "currentDir": self.currentDir,
                "held": self.held
            },
            "nodes": nodes_list,
        }

        return json.dumps(payload, indent=2)      

    def identifyElements(self, imgName):
        input_path = f"{Path(__file__).parent}/testOutput/{imgName}_resized.jpg"
        model = YOLO(f"{Path(__file__).parent}/test_v5/weights/best.pt")
        img = cv2.imread(input_path)
        if img is None:
            print(f"No se pudo cargar la imagen en {input_path}")
            exit()

        results = model.predict(img, save=False, project=f"{Path(__file__).parent}/testOutput/", name='example', conf=0.3, verbose=False)

        baseCoords = list(self.currentPos)
        nombres_clases = results[0].names
        mostRestrictiveDoor = 5
        elements = []
        for box in results[0].boxes:
            e = {}
            x_center, y_center, width, height = box.xywhn[0].tolist()

            clase_id = int(box.cls[0].item())
            nombreObj = nombres_clases[clase_id]
            
            nombreLimpio = nombreObj.split("_")[0]

            distancia = estimar_distancia(nombreLimpio, [x_center, y_center, width, height])

            if distancia is not None:
                distancia_m = float(distancia)
                celda = DISTANCES_DICTIONARY[nombreLimpio].index(distancia_m) + 1
            else:
                distancia_m = None
                celda = None

            if celda is not None:
                if(self.currentDir == 'u'):
                    c = (baseCoords[0], baseCoords[1] + celda)
                elif(self.currentDir == 'd'):
                    c = (baseCoords[0], baseCoords[1] - celda)
                elif(self.currentDir == 'r'):
                    c = (baseCoords[0] + celda, baseCoords[1])
                elif(self.currentDir == 'l'):
                    c = (baseCoords[0] - celda, baseCoords[1])

                typeTile = NAMES_TO_TYPES[nombreLimpio]
                if(typeTile == 'K' or typeTile == 'D'):
                    id  = NAMES_TO_IDS[nombreObj.split("_")[1]]
                else:
                    id = -1

                if(typeTile == 'D'):
                    if(self.currentDir == 'u' or self.currentDir == 'd'):
                        distToDoor = abs(c[1] - baseCoords[1])
                    else:
                        distToDoor = abs(c[0] - baseCoords[0])

                    mostRestrictiveDoor = min(mostRestrictiveDoor, distToDoor)

                e["c"] = c
                e["type"] = typeTile
                e["id"] = id

                elements.append(e)
        
        return mostRestrictiveDoor, elements
                

    def correct(self, mostRestrictiveDoor, elements):
        baseCoords = list(self.currentPos)
        for i in range(mostRestrictiveDoor):
            if(self.currentDir == 'u'):
                baseCoords[1] += 1
            elif(self.currentDir == 'd'):
                baseCoords[1] -= 1
            elif(self.currentDir == 'r'):
                baseCoords[0] += 1
            elif(self.currentDir == 'l'):
                baseCoords[0] -= 1

            coords = tuple(baseCoords)
            if coords in self.map:
                self.map[coords].explored = True
            else:
                break

        if not elements:
            return

        for e in elements:
            c = e["c"]
            typeTile = e["type"]
            id = e["id"]

            while(c not in self.map and (typeTile == 'K' or typeTile == '?')):
                if self.currentDir == 'u':
                    c = (c[0], c[1] - 1)
                elif self.currentDir == 'd':
                    c = (c[0], c[1] + 1)
                elif self.currentDir == 'r':
                    c = (c[0] - 1, c[1])
                elif self.currentDir == 'l':
                    c = (c[0] + 1, c[1])

            if(c in self.map and self.map[c].explored and self.map[c].typeTile == 'X'):
                self.map[c].typeTile = typeTile

                if typeTile == 'D':
                    self.poi = [p for p in self.poi if p.tile != self.map[c]]

                if (typeTile == 'K' or typeTile == 'D') and self.map[c].id == -1:
                    self.map[c].id = id
                    self.map[c].locked = True

                    pair = False
                    for fID in self.foundIDs:
                        if fID.tile.id == id and typeTile == 'K':
                            self.prioritypoi.append(POI(self.map[c], self.currentDir, 1))
                            self.map[c].locked = False
                            self.prioritypoi.append(fID)
                            fID.tile.locked = False
                            self.foundIDs.remove(fID)
                            pair = True
                            break

                        elif fID.tile.id == id and typeTile == 'D':
                            self.prioritypoi.append(fID)
                            fID.tile.locked = False
                            self.prioritypoi.append(POI(self.map[c], self.currentDir, 1))
                            self.map[c].locked = False
                            self.foundIDs.remove(fID)
                            pair = True
                            break

                    if pair is False:
                        self.addPOI(self.map[c], self.currentDir, True)
                        
                else:
                    self.prioritypoi.append(POI(self.map[c], self.currentDir, 0))

def find_wall_errors(labGT, labHomo):
    errors = []
    
    for coords, gt_node in labGT.map.items():
        if coords not in labHomo.map:
            errors.append(f"  [!] Missing Tile: GT found a tile at {coords}, but Homo missed it.")
            continue

        homo_node = labHomo.map[coords]

        for d in ['u', 'd', 'l', 'r']:
            gt_is_wall = (getattr(gt_node, d) == 'Wall')
            homo_is_wall = (getattr(homo_node, d) == 'Wall')

            if gt_is_wall != homo_is_wall:
                errors.append(f"  [-] Mismatch at Tile {coords} | Dir '{d}': GT says Wall={gt_is_wall}, Homo says Wall={homo_is_wall}")
                
    return errors

def estimar_distancia(clase, bbox):
    x, y, w, h = bbox
    margen = 0.01

    if abs(x - 0.5) > 0.15:
      return None

    for distancia_real in reversed(list(OBJECT_METRICS[clase])):
      wMed = OBJECT_METRICS[clase][distancia_real]["w_med"]
      wDif = OBJECT_METRICS[clase][distancia_real]["w_dif"]

      hMed = OBJECT_METRICS[clase][distancia_real]["h_med"]
      hDif = OBJECT_METRICS[clase][distancia_real]["h_dif"]

      if abs(w - wMed) <= ((wDif / 2)+ margen) and abs(h - hMed) <= ((hDif / 2)+ margen):
          return distancia_real

    return None

def start():      
    lab = Labyrinth(3)
    iN = Node()
    lab.currentNode = iN
    lab.map[(0, 0)] = iN
    iN.connect(0, 0)
    lab.mapRemain -= 1

    iN.setTile(lab)
    lab.poi.pop()
    iN.explored = True
    return lab

#Called whenever we get an image to analyze (aka b/w homography + reduced image for yolo)
def analyze(lab, imgName):
    print(f"Recieved input: ")
    mostRestrictiveDoor, elements = lab.identifyElements(imgName)
    lab.updateFromImage(imgName, mostRestrictiveDoor)
    lab.correct(mostRestrictiveDoor, elements)
    destinationType, finalCommands = lab.selectNextPOI()

    if(destinationType == 'K' or destinationType == '?'):
        print(f"He ido a la {destinationType} de {lab.currentPos}")
        analyze(lab, "wall")
    elif(destinationType == 'D'):
        print(f"He ido a la {destinationType} de {lab.currentPos}")
        lab.currentNode.setTile(lab)
        analyze(lab, "img_7")

    return destinationType, finalCommands
